Zeppelin500/MBusino/sensostar_dongle/picture2.jpg

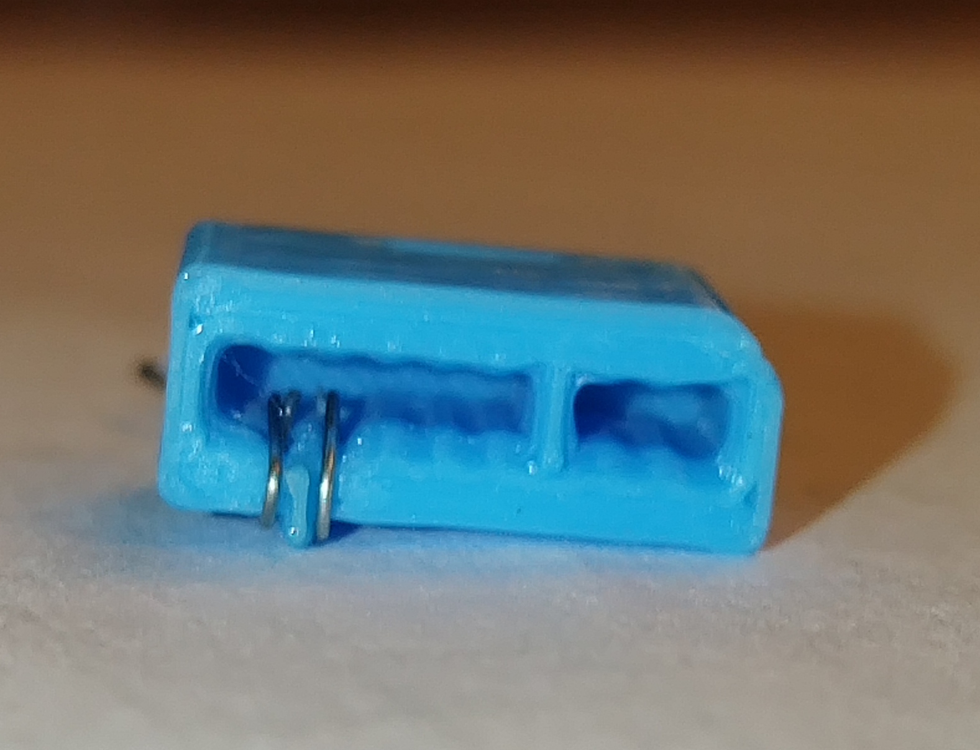
sensostar_dongle/picture2.jpg
