Zeppelin500/MBusino/sensostar_dongle/picture4.jpg

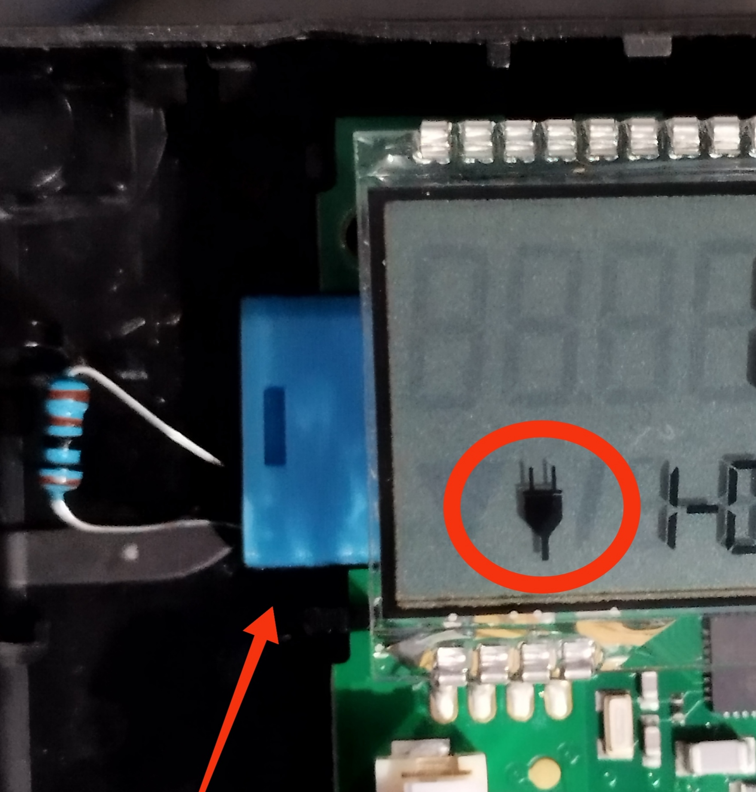
sensostar_dongle/picture4.jpg
