Zeppelin500/MBusino/sensostar_dongle/picture.png

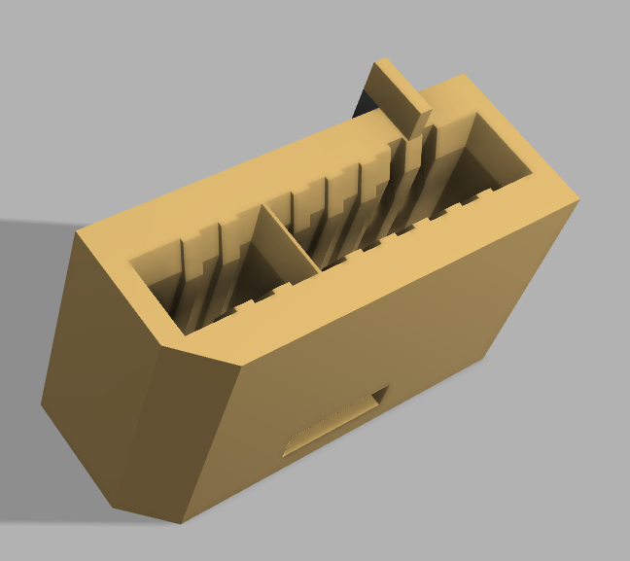
sensostar_dongle/picture.png
