Zeppelin500/MBusino/src/MBusino5S/autodiscover.h

struct autodiscover {
  char bufferValue[1024] = {0};
  char bufferTopic[100] = {0};
  char haName[30] = {0};
  char haUnits[30] = {0};
  char stateClass[30] = {0};
  char deviceClass[30] = {0};
  char deviceClassString[50] = {0};
} adVariables; // home assistand auto discover

const char bmeValue[4][12] = {"temperature","pressure","altitude","humidity"};
const char bmeDeviceClass[4][12] = {"temperature","pressure","distance","humidity"};
const char bmeUnits[4][5] = {"°C","mbar","m","%"};

//const char vs[4] = "_vs"; //placeholder for insert "_vs" for valuestring is used instead of value
//const char[4] noVs = {0}; //empty, no Valuestring

const char adValueMbus[] PROGMEM = R"rawliteral({"unique_id":"%s_%u_%u_%s","default_entity_id":"sensor.%s_%u_%u_%s","state_topic":"%s/MBus/SlaveAddress%u/%u_%s","name":"Addr%u_%u_%s","value_template":"{{value_json}}","unit_of_meas":"%s","state_class":"%s","device":{"ids": ["%s"],"name":"%s","manufacturer": "MBusino","mdl":"V%s"},%s"expire_after":%u,"availability_topic":"%s/status","payload_available":"online","payload_not_available":"offline","availability_mode":"all"})rawliteral";
const char adTopicMbus[] PROGMEM = R"rawliteral(homeassistant/sensor/%s/%u_%u_%s/config)rawliteral";

const char adValueSensor[] PROGMEM = R"rawliteral({"unique_id":"%s_Sensor%u","default_entity_id":"sensor.%s_Sensor%u","state_topic":"%s/OneWire/S%u","name":"Sensor%u","value_template":"{{value_json}}","unit_of_meas":"°C","state_class":"measurement","device":{"ids": ["%s"],"name":"%s","manufacturer": "MBusino","mdl":"V%s"},"device_class":"temperature","expire_after":%u,"availability_topic":"%s/status","payload_available":"online","payload_not_available":"offline","availability_mode":"all"})rawliteral";
const char adTopicSensor[] PROGMEM = R"rawliteral(homeassistant/sensor/%s/Sensor%u/config)rawliteral";

const char adValueBME[] PROGMEM = R"rawliteral({"unique_id":"%s__BME_%s","default_entity_id":"sensor.%s_BME_%s","state_topic":"%s/bme/%s","name":"%s","value_template":"{{value_json}}","unit_of_meas":"%s","state_class":"measurement","device":{"ids": ["%s"],"name":"%s","manufacturer": "MBusino","mdl":"V%s"},"device_class":"%s","expire_after":%u,"availability_topic":"%s/status","payload_available":"online","payload_not_available":"offline","availability_mode":"all"})rawliteral";
const char adTopicBME[] PROGMEM = R"rawliteral(homeassistant/sensor/%s/%s/config)rawliteral";

void haHandoverMbus(uint8_t haCounter, bool engelmann, uint8_t address){ // haCounter is the "i+1" at the for() in main

  if(adVariables.deviceClass[0] != 0){
    strcpy(adVariables.deviceClassString,String("\"device_class\": \"" + String(adVariables.deviceClass) + "\",").c_str());
  }
  sprintf(adVariables.bufferValue,adValueMbus,userData.mbusinoName,address,haCounter,adVariables.haName,userData.mbusinoName,address,haCounter,adVariables.haName,userData.mbusinoName,address,haCounter,adVariables.haName,address,haCounter,adVariables.haName,adVariables.haUnits,adVariables.stateClass,userData.mbusinoName,userData.mbusinoName,MBUSINO_VERSION,adVariables.deviceClassString,userData.mbusInterval / 1000 * 3 * (userData.mbusSlaves > 0 ? userData.mbusSlaves : 1),userData.mbusinoName);
  sprintf(adVariables.bufferTopic,adTopicMbus,userData.mbusinoName,address,haCounter,adVariables.haName);
  client.publish(adVariables.bufferTopic, adVariables.bufferValue, true); 

  if(haCounter == 4 && engelmann == true){  // Sensostar Bugfix --> comment it out if you use not a Sensostar   
    sprintf(adVariables.bufferValue,adValueMbus,userData.mbusinoName,address,haCounter,"power_calc",userData.mbusinoName,address,haCounter,"power_calc",userData.mbusinoName,address,haCounter,"power_calc",address,haCounter,"power_calc",adVariables.haUnits,adVariables.stateClass,userData.mbusinoName,userData.mbusinoName,MBUSINO_VERSION,adVariables.deviceClassString,userData.mbusInterval / 1000 * 3 * (userData.mbusSlaves > 0 ? userData.mbusSlaves : 1),userData.mbusinoName);
    sprintf(adVariables.bufferTopic,adTopicMbus,userData.mbusinoName,address,haCounter,"power_calc");
    client.publish(adVariables.bufferTopic, adVariables.bufferValue, true);                   
  } 

  adVariables.bufferTopic[0] = 0;
  adVariables.bufferValue[0] = 0;
  adVariables.deviceClass[0] = 0;
  adVariables.deviceClassString[0] = 0;
  adVariables.stateClass[0] = 0;
  adVariables.haUnits[0] = 0;
}

void haHandoverOw(uint8_t haCounter){
  sprintf(adVariables.bufferValue,adValueSensor,userData.mbusinoName,haCounter,userData.mbusinoName,haCounter,userData.mbusinoName,haCounter,haCounter,userData.mbusinoName,userData.mbusinoName,MBUSINO_VERSION,userData.sensorInterval / 1000 * 3,userData.mbusinoName);
  sprintf(adVariables.bufferTopic,adTopicSensor,userData.mbusinoName,haCounter);
  client.publish(adVariables.bufferTopic, adVariables.bufferValue, true); 
  adVariables.bufferTopic[0] = 0;
  adVariables.bufferValue[0] = 0;
}

void haHandoverBME(){
  for(uint8_t i=0; i<4;i++){  
    sprintf(adVariables.bufferValue,adValueBME,userData.mbusinoName,bmeValue[i],userData.mbusinoName,bmeValue[i],userData.mbusinoName,bmeValue[i],bmeValue[i],bmeUnits[i],userData.mbusinoName,userData.mbusinoName,MBUSINO_VERSION,bmeDeviceClass[i],userData.sensorInterval / 1000 * 3,userData.mbusinoName);
    sprintf(adVariables.bufferTopic,adTopicBME,userData.mbusinoName,bmeValue[i]);
    client.publish(adVariables.bufferTopic, adVariables.bufferValue, true); 
    adVariables.bufferTopic[0] = 0;
    adVariables.bufferValue[0] = 0;
  }
}

// --- Header autodiscovery ---
struct headerAdField {
  const char* jsonKey;
};

static const headerAdField headerAdFields[] = {
  {"address"},
  {"id"},
  {"manufacturer"},
  {"medium"},
  {"version"},
  {"status"},
  {"access_counter"},
  {"battery_low"},
  {"temporary_error"},
  {"permanent_error"},
};

#define HEADER_AD_FIELDS_COUNT (sizeof(headerAdFields) / sizeof(headerAdFields[0]))

const char adValueHeader[] PROGMEM = R"rawliteral({"unique_id":"%s_header_%u_%s","default_entity_id":"sensor.%s_header_%u_%s","state_topic":"%s/MBus/SlaveAddress%u/header/%s","name":"Addr%u_%s","value_template":"{{value}}","device":{"ids": ["%s"],"name":"%s","manufacturer": "MBusino","mdl":"V%s"},"availability_topic":"%s/status","payload_available":"online","payload_not_available":"offline","availability_mode":"all"})rawliteral";
const char adTopicHeader[] PROGMEM = R"rawliteral(homeassistant/sensor/%s/header_%u_%s/config)rawliteral";

void haHandoverHeader(uint8_t address){
  for(uint8_t i = 0; i < HEADER_AD_FIELDS_COUNT; i++){
    sprintf(adVariables.bufferValue, adValueHeader,
      userData.mbusinoName, address, headerAdFields[i].jsonKey,
      userData.mbusinoName, address, headerAdFields[i].jsonKey,
      userData.mbusinoName, address, headerAdFields[i].jsonKey,
      address, headerAdFields[i].jsonKey,
      userData.mbusinoName, userData.mbusinoName, MBUSINO_VERSION,
      userData.mbusinoName);
    sprintf(adVariables.bufferTopic, adTopicHeader, userData.mbusinoName, address, headerAdFields[i].jsonKey);
    client.publish(adVariables.bufferTopic, adVariables.bufferValue, true);
    adVariables.bufferTopic[0] = 0;
    adVariables.bufferValue[0] = 0;
  }
}

// --- Header MQTT publish ---
enum HeaderFieldType { HT_STR, HT_INT, HT_HEX, HT_BOOL_NESTED };

struct headerPublishField {
  const char* jsonKey;
  HeaderFieldType type;
};

static const headerPublishField headerPublishFields[] = {
  {"address",        HT_INT},
  {"id",             HT_STR},
  {"manufacturer",   HT_STR},
  {"medium",         HT_STR},
  {"version",        HT_INT},
  {"status",         HT_HEX},
  {"access_counter", HT_INT},
};

#define HEADER_PUBLISH_COUNT (sizeof(headerPublishFields) / sizeof(headerPublishFields[0]))

static const char* headerStatusKeys[] = {"battery_low", "temporary_error", "permanent_error"};
#define HEADER_STATUS_COUNT (sizeof(headerStatusKeys) / sizeof(headerStatusKeys[0]))



/*
char* getStateClass(const char* unit) {
  if (this->unit == "C") {
      return "measurement";
  }else if (this->unit == "K") {
      return "measurement";
  }else if (this->unit == "W") {
      return "measurement";
  }else if(this->unit =="Wh") {
      return "total";
  }else if(this->unit=="kWh"){
      return "total";
  }else if(this->unit=="m3") {
      return "total";
  }else if(this->unit =="m3/h"){
      return "measurement";
  } else {
      return String("");
  }
}

String getDeviceClass() {
    if (this->unit == "C") {
        return "temperature";
    }else if (this->unit == "K") {
        return "temperature";
    }else if (this->unit == "W") {
        return "power";
    }else if(this->unit =="Wh") {
        return "energy";
    }else if(this->unit=="kWh"){
        return "energy";
    }else if(this->unit=="m3") {
        return "water";
    }else if(this->unit =="m3/h"){
        return String("");
    } else {
        return String("");
    }
}


///######## Device.h #####################################
#include <vector>
class Device {
public:

    Device() = default;
    String toJsonString(String mbusinoName) const {
        String oss;
        oss +=  "{";
        oss +=   "\"ids\":  [";
        oss +=    "\""+mbusinoName+"\"";
        oss +=    "],";
        oss +=    "\"name\": \""+mbusinoName+"\",";
        oss +=    "\"mdl\": \"MBusino v.070\"";
        oss += "}";
        return oss;
    }
};

///######## MBusTopic.h #####################################
#include "SensorData.h"

class MBusTopic {
public:
    String topic;
    String value;
    String unit;
    String name;

    MBusTopic(String t) : topic(t), value(""), unit("") {
        name = getLastTopicPart(t);
    }

    void setValue(String v) {
        value = v;
    }

    void setUnit(String u) {
        unit = u;
    }

private:
    const char *getLastTopicPart(String curTopic) {
        const char *lastSlash = strrchr(curTopic.c_str(), '/'); // Suche den letzten Slash

        if (lastSlash != nullptr) {
            // Rückgabe des Zeigers auf den Anfang des letzten Teils des Topics
            return lastSlash + 1;
        } else {
            // Wenn kein Slash gefunden wurde, bedeutet das, dass der ganze String das Topic ist
            return curTopic.c_str();
        }
    }

    bool isValid() {
        if (this->value != nullptr && this->unit != nullptr) {
            return true;
        } else {
            return false;
        }
    }

private:
    String getUnitOfMeassuremetn() {
        if (this->unit == "C") {
            return "°C";
        }else if (this->unit == "K") {
            return "K";
        }else if (this->unit == "W") {
            return "W";
        }else if(this->unit =="Wh") {
            return "Wh";
        }else if(this->unit=="kWh"){
            return "kWh";
        }else if(this->unit=="m3") {
            return "m³";
        }else if(this->unit =="m3/h"){
            return "m³/h";
        } else {
            return String("");
        }
    }
private:
    String getStateClass() {
        if (this->unit == "C") {
            return "measurement";
        }else if (this->unit == "K") {
            return "measurement";
        }else if (this->unit == "W") {
            return "measurement";
        }else if(this->unit =="Wh") {
            return "total";
        }else if(this->unit=="kWh"){
            return "total";
        }else if(this->unit=="m3") {
            return "total";
        }else if(this->unit =="m3/h"){
            return "measurement";
        } else {
            return String("");
        }
    }
private:
    String getDeviceClass() {
        if (this->unit == "C") {
            return "temperature";
        }else if (this->unit == "K") {
            return "temperature";
        }else if (this->unit == "W") {
            return "power";
        }else if(this->unit =="Wh") {
            return "energy";
        }else if(this->unit=="kWh"){
            return "energy";
        }else if(this->unit=="m3") {
            return "water";
        }else if(this->unit =="m3/h"){
            return String("");
        } else {
            return String("");
        }
    }


public:
    SensorData toSensorData(String basic) {
        SensorData sensorData;
        sensorData.unique_id = basic + "_" + this->name;
        sensorData.object_id = basic + "_" + this->name;
        sensorData.state_topic = this->topic;
        sensorData.name = this->name;
        sensorData.value_template = "{{value_json if value_json is defined else 0}}";
        sensorData.unit_of_meas = getUnitOfMeassuremetn();
        sensorData.state_class = getStateClass();
        sensorData.device_class = getDeviceClass();
        sensorData.availability_mode = "all";
        return sensorData;
    }
};

///######## MBusTopicService.h #####################################
#include "SensorData.h"

class MBusTopic {
public:
    String topic;
    String value;
    String unit;
    String name;

    MBusTopic(String t) : topic(t), value(""), unit("") {
        name = getLastTopicPart(t);
    }

    void setValue(String v) {
        value = v;
    }

    void setUnit(String u) {
        unit = u;
    }

private:
    const char *getLastTopicPart(String curTopic) {
        const char *lastSlash = strrchr(curTopic.c_str(), '/'); // Suche den letzten Slash

        if (lastSlash != nullptr) {
            // Rückgabe des Zeigers auf den Anfang des letzten Teils des Topics
            return lastSlash + 1;
        } else {
            // Wenn kein Slash gefunden wurde, bedeutet das, dass der ganze String das Topic ist
            return curTopic.c_str();
        }
    }

    bool isValid() {
        if (this->value != nullptr && this->unit != nullptr) {
            return true;
        } else {
            return false;
        }
    }

private:
    String getUnitOfMeassuremetn() {
        if (this->unit == "C") {
            return "°C";
        }else if (this->unit == "K") {
            return "K";
        }else if (this->unit == "W") {
            return "W";
        }else if(this->unit =="Wh") {
            return "Wh";
        }else if(this->unit=="kWh"){
            return "kWh";
        }else if(this->unit=="m3") {
            return "m³";
        }else if(this->unit =="m3/h"){
            return "m³/h";
        } else {
            return String("");
        }
    }
private:
    String getStateClass() {
        if (this->unit == "C") {
            return "measurement";
        }else if (this->unit == "K") {
            return "measurement";
        }else if (this->unit == "W") {
            return "measurement";
        }else if(this->unit =="Wh") {
            return "total";
        }else if(this->unit=="kWh"){
            return "total";
        }else if(this->unit=="m3") {
            return "total";
        }else if(this->unit =="m3/h"){
            return "measurement";
        } else {
            return String("");
        }
    }
private:
    String getDeviceClass() {
        if (this->unit == "C") {
            return "temperature";
        }else if (this->unit == "K") {
            return "temperature";
        }else if (this->unit == "W") {
            return "power";
        }else if(this->unit =="Wh") {
            return "energy";
        }else if(this->unit=="kWh"){
            return "energy";
        }else if(this->unit=="m3") {
            return "water";
        }else if(this->unit =="m3/h"){
            return String("");
        } else {
            return String("");
        }
    }


public:
    SensorData toSensorData(String basic) {
        SensorData sensorData;
        sensorData.unique_id = basic + "_" + this->name;
        sensorData.object_id = basic + "_" + this->name;
        sensorData.state_topic = this->topic;
        sensorData.name = this->name;
        sensorData.value_template = "{{value_json if value_json is defined else 0}}";
        sensorData.unit_of_meas = getUnitOfMeassuremetn();
        sensorData.state_class = getStateClass();
        sensorData.device_class = getDeviceClass();
        sensorData.availability_mode = "all";
        return sensorData;
    }
};
//######################### SensorData.h ###############################################################
#include <vector>
#include "Device.h"

class SensorData {
public:
    String unique_id;
    String object_id;
    String state_topic;
    String name;
    String value_template;
    String unit_of_meas;
    String state_class;
    Device device;
    String availability_mode;
    String device_class;

    SensorData() = default;

public:
    String toJsonString(String mbusinoName) const {
        String oss;
        oss += "{";
        oss += "\"unique_id\":\"" + unique_id + "\",";
        oss += "\"object_id\":\"" + object_id + "\",";
        oss += "\"state_topic\":\"" + state_topic + "\",";
        oss += "\"name\":\"" + name + "\",";
        oss += "\"value_template\":\"" + value_template + "\",";
        if (!unit_of_meas.isEmpty()) {
            oss += "\"unit_of_meas\":\"" + unit_of_meas + "\",";
        }
        // checking state_class for null and empty, if nothing is present then no entry is made in JSON
        if (!state_class.isEmpty()) {
            oss += "\"state_class\":\"" + state_class + "\",";
        }
        oss += "\"device\":" + device.toJsonString(mbusinoName) + ",";
        if (!device_class.isEmpty()) {
            oss += "\"device_class\":\"" + device_class+ "\",";
        }
        oss += "\"availability_mode\":\"" + availability_mode + "\"";

        oss += "}";
        return oss;
    }

};
*/
