Zeppelin500/MBusino/src/MBusinoNano5S/networkEvents.h

// WARNING: onEvent is called from a separate FreeRTOS task (thread)!
void onEvent(arduino_event_id_t event) {
  switch (event) {
    case ARDUINO_EVENT_ETH_START:
      Serial.println("ETH Started");
      // The hostname must be set after the interface is started, but needs
      // to be set before DHCP, so set it from the event handler thread.
//      ETH.setHostname(String(String(userData.mbusinoName)+"-eth").c_str());
      ETH.setHostname(userData.mbusinoName);
      //ETH.setLinkSpeed(10);
      break;
    case ARDUINO_EVENT_ETH_CONNECTED: 
      Serial.println("ETH Connected"); 
      eth_connected = true;
      timerETHmessage = millis();
      timerNetworkChange = millis();
      break;
    case ARDUINO_EVENT_ETH_GOT_IP:
      Serial.println("ETH Got IP");
      Serial.println(ETH);
      eth_connected = true;
      gotIP = true;
      break;
    case ARDUINO_EVENT_ETH_LOST_IP:
      Serial.println("ETH Lost IP");
      eth_connected = false;
      Serial.println("Lost ETH IP, restart soon");
      timerReboot = millis();
      waitForRestart = true;
      break;
    case ARDUINO_EVENT_ETH_DISCONNECTED:
      Serial.println("ETH Disconnected");
      eth_connected = false;
      gotIP = false;
      break;
    case ARDUINO_EVENT_ETH_STOP:
      Serial.println("ETH Stopped");
      eth_connected = false;
      break;
    default: break;
  }
}


// WARNING: This function is called from a separate FreeRTOS task (thread)!
void WiFiEvent(WiFiEvent_t event) {
  Serial.printf("[WiFi-event] event: %d\n", event);

  switch (event) {
    case ARDUINO_EVENT_WIFI_READY:               Serial.println("WiFi interface ready"); break;
    case ARDUINO_EVENT_WIFI_SCAN_DONE:           Serial.println("Completed scan for access points"); break;
    case ARDUINO_EVENT_WIFI_STA_START:           Serial.println("WiFi client started"); break;
    case ARDUINO_EVENT_WIFI_STA_STOP:            Serial.println("WiFi clients stopped"); break;
    case ARDUINO_EVENT_WIFI_STA_CONNECTED:
      Serial.println("Connected to access point"); 
      break;
    case ARDUINO_EVENT_WIFI_STA_DISCONNECTED:    
      Serial.println("Disconnected from WiFi access point"); 
      wifiReconnect = true;
      timerWifiReconnect = millis();
    case ARDUINO_EVENT_WIFI_STA_AUTHMODE_CHANGE: Serial.println("Authentication mode of access point has changed"); break;
    case ARDUINO_EVENT_WIFI_STA_GOT_IP:
      Serial.print("Obtained IP address: ");
      Serial.println(WiFi.localIP());
      break;
    case ARDUINO_EVENT_WIFI_STA_LOST_IP:        Serial.println("Lost IP address and IP address is reset to 0"); break;
    case ARDUINO_EVENT_WPS_ER_SUCCESS:          Serial.println("WiFi Protected Setup (WPS): succeeded in enrollee mode"); break;
    case ARDUINO_EVENT_WPS_ER_FAILED:           Serial.println("WiFi Protected Setup (WPS): failed in enrollee mode"); break;
    case ARDUINO_EVENT_WPS_ER_TIMEOUT:          Serial.println("WiFi Protected Setup (WPS): timeout in enrollee mode"); break;
    case ARDUINO_EVENT_WPS_ER_PIN:              Serial.println("WiFi Protected Setup (WPS): pin code in enrollee mode"); break;
    case ARDUINO_EVENT_WIFI_AP_START:           Serial.println("WiFi access point started"); break;
    case ARDUINO_EVENT_WIFI_AP_STOP:            Serial.println("WiFi access point  stopped"); break;
    case ARDUINO_EVENT_WIFI_AP_STACONNECTED:    Serial.println("Client connected"); break;
    case ARDUINO_EVENT_WIFI_AP_STADISCONNECTED: Serial.println("Client disconnected"); break;
    case ARDUINO_EVENT_WIFI_AP_STAIPASSIGNED:   Serial.println("Assigned IP address to client"); break;
    case ARDUINO_EVENT_WIFI_AP_PROBEREQRECVED:  Serial.println("Received probe request"); break;
    case ARDUINO_EVENT_WIFI_AP_GOT_IP6:         Serial.println("AP IPv6 is preferred"); break;
    case ARDUINO_EVENT_WIFI_STA_GOT_IP6:        Serial.println("STA IPv6 is preferred"); break;
    case ARDUINO_EVENT_ETH_GOT_IP6:             Serial.println("Ethernet IPv6 is preferred"); break;
    case ARDUINO_EVENT_ETH_START:               Serial.println("Ethernet started"); break;
    case ARDUINO_EVENT_ETH_STOP:                Serial.println("Ethernet stopped"); break;
    case ARDUINO_EVENT_ETH_CONNECTED:           Serial.println("Ethernet connected"); break;
    case ARDUINO_EVENT_ETH_DISCONNECTED:        Serial.println("Ethernet disconnected"); break;
    case ARDUINO_EVENT_ETH_GOT_IP:              Serial.println("Obtained IP address"); break;
    default:                                    break;
  }
}
