Zeppelin500/MBusino/playground/multible_slaves/MBusino_naked_scan/MBusino_naked_scan.ino

/*
# MBusino_naked --> only M-Bus 

21 October 2023: new code based at MBusino with payload library. You find the old "Sensostar only" code in archive.

documentation see MBusino

## Licence
****************************************************
This program is free software: you can redistribute it and/or modify it under the terms of the GNU General Public License as published by
the Free Software Foundation, either version 3 of the License, or (at your option) any later version. This program is distributed in the hope that it will be useful,
but WITHOUT ANY WARRANTY; without even the implied warranty of MERCHANTABILITY or FITNESS FOR A PARTICULAR PURPOSE.  See the GNU General Public License for more details.
You should have received a copy of the GNU General Public License along with this program.  If not, see <http://www.gnu.org/licenses/>.
****************************************************
*/

#include <EspMQTTClient.h>

#include <credentials.h>  // <-- comment it out if you use no library for WLAN access data.

#include <MBusinoLib.h>  // Library for decode M-Bus
#include "ArduinoJson.h"
#include <EEPROM.h>

#define MBUSINO_NAME "SBusino" // If you have more MBusinos, rename it inside quote marks, or it cause some network and MQTT problems. Also you cant reach your MBusino from Arduino IDE

#define MBUS_BAUD_RATE 2400
#define MBUS_ADDRESS 0xFE  // brodcast
#define MBUS_TIMEOUT 1000  // milliseconds
#define MBUS_DATA_SIZE 510
#define MBUS_GOOD_FRAME true
#define MBUS_BAD_FRAME false

#define MBUS_FRAME_SHORT_START          0x10
#define MBUS_FRAME_LONG_START           0x68
#define MBUS_FRAME_STOP                 0x16

#define MBUS_CONTROL_MASK_SND_NKE       0x40
#define MBUS_CONTROL_MASK_DIR_M2S       0x40
#define MBUS_ADDRESS_NETWORK_LAYER      0xFE

#define MBUS_ACK                        0xE5


EspMQTTClient client(
  WLAN_SSID,       // WLAN-SSID in quote marks "mySSID"
  WLAN_PASSWORD,   // WLAN Password in quote marks "myPassword"
  MQTT_Broker,     // MQTT Broker IP address in quote marks "192.168.x.x"
  "MQTTUsername",  // Can be omitted if not needed
  "MQTTPassword",  // Can be omitted if not needed -- also password for OTA Update with Arduino IDE 2
  MBUSINO_NAME,    // Client name that uniquely identify your device
  1883             // The MQTT port, default to 1883. this line can be omitted
);


unsigned long loop_start = 0;
unsigned long last_loop = 0;
bool firstrun = true;
int Startadd = 0x13;  // Start address for decoding
char jsonstring[6144] = { 0 };

int MbusInterval = 5000;           // interval for MBus request in milliseconds

unsigned long timerMbus = 0;

void mbus_normalize(byte address);
void mbus_request_data(byte address);
void mbus_short_frame(byte address, byte C_field);
bool mbus_get_response(byte *pdata, unsigned char len_pdata);
void calibrationAverage();
void calibrationSensor(uint8_t sensor);
void calibrationValue(float value);
void calibrationBME();
void calibrationSet0();

uint8_t scanAddress = 10;
unsigned long scanTimer = 0;
uint8_t scanned = false;
bool setAdress = true;
unsigned long setTimer = 0;
bool normalize = true;
unsigned long setTimer2 = 0;
bool normalize2 = true;

void setup() {
  Serial.begin(2400, SERIAL_8E1);

  // Optional functionalities of EspMQTTClient
  client.enableHTTPWebUpdater("/update");                                           // Enable the web updater. User and password default to values of MQTTUsername and MQTTPassword. These can be overridded with enableHTTPWebUpdater("user", "password").
  client.enableOTA();                                                      // Enable OTA (Over The Air) updates. Password defaults to MQTTPassword. Port is the default OTA port. Can be overridden with enableOTA("password", port).
  client.enableLastWillMessage(MBUSINO_NAME"/lastwill", "I am going offline");  // You can activate the retain flag by setting the third parameter to true
  client.setMaxPacketSize(6000);

  scanTimer = millis()+10000;
  

}

// This function is called once everything is connected (Wifi and MQTT)
// WARNING : YOU MUST IMPLEMENT IT IF YOU USE EspMQTTClient
void onConnectionEstablished() {  // send a message to MQTT broker if connected.
  client.publish(MBUSINO_NAME"/start", "bin hoch gefahren, WLAN und MQTT seht ");  
}

void loop() {
  client.loop();  //MQTT Funktion
  loop_start = millis();
   while (Serial.available() && (millis() - setTimer) < 7000) { // Serial buffer leeren
      byte val = Serial.read();
      client.publish(String(MBUSINO_NAME "/serialAviable/recieved_" + String(scanAddress)), String(val)); 
    }
  if((millis() - setTimer) > 7000 && normalize == true){  
    
    mbus_normalize(0xFD);
    client.publish(String(MBUSINO_NAME"/normalize2"), "done");
    normalize = false;
  }
  if((millis() - setTimer2) > 8000 && normalize2 == true){  
    mbus_normalize(0xFD);
    if (Serial.available()) {
      byte val = Serial.read();
      client.publish(String(MBUSINO_NAME "/normalized2/recieved_" + String(scanAddress)), String(val)); 
    }
    client.publish(String(MBUSINO_NAME"/normalize2"), "done");
    normalize2 = false;
  }

  if((millis() - setTimer) > 10000 && setAdress == true){
    mbus_set_address(0x05, 0x00);
    client.publish(String(MBUSINO_NAME"/setAdress"), "done");
    setAdress = false;
    scanTimer = millis(); 
  }
  if((millis() - scanTimer) > 1000 && scanned == false && setAdress == false){
    client.publish(String(MBUSINO_NAME"/scanning/" + String(scanAddress)), "done");  
    mbus_normalize(scanAddress);
    scanTimer = millis(); 
    scanned = true;
  }
  if((millis() - scanTimer) > 1000 && scanned == true && setAdress == false){
    client.publish(String(MBUSINO_NAME "/reading/" + String(scanAddress)), "done");  
    scanTimer = millis();
    if (Serial.available()) {
      byte val = Serial.read();
      client.publish(String(MBUSINO_NAME "/reading/recieved_" + String(scanAddress)), String(val)); 
    }
  scanned = false;
  scanAddress--;
  }
   
 
}

void mbus_normalize(byte address) {
  mbus_short_frame(address,0x40);
}

void mbus_request_data(byte address) {
  mbus_short_frame(address, 0x5b);
}

void mbus_short_frame(byte address, byte C_field) {
  byte data[6];

  data[0] = 0x10;
  data[1] = C_field;
  data[2] = address;
  data[3] = data[1] + data[2];
  data[4] = 0x16;
  data[5] = '\0';

  Serial.write((char *)data,5);
}

bool mbus_get_response(byte *pdata, unsigned char len_pdata) {
  byte bid = 0;             // current byte of response frame
  byte bid_end = 255;       // last byte of frame calculated from length byte sent
  byte bid_checksum = 255;  // checksum byte of frame (next to last)
  byte len = 0;
  byte checksum = 0;
  bool long_frame_found = false;
  bool complete_frame = false;
  bool frame_error = false;

  unsigned long timer_start = millis();
  while (!frame_error && !complete_frame && (millis() - timer_start) < MBUS_TIMEOUT) {
    while (Serial.available()) {
      byte received_byte = (byte)Serial.read();

      // Try to skip noise
      if (bid == 0 && received_byte != 0xE5 && received_byte != 0x68) {
        continue;
      }

      if (bid > len_pdata) {
        return MBUS_BAD_FRAME;
      }
      pdata[bid] = received_byte;

      // Single Character (ACK)
      if (bid == 0 && received_byte == 0xE5) {
        return MBUS_GOOD_FRAME;
      }

      // Long frame start
      if (bid == 0 && received_byte == 0x68) {
        long_frame_found = true;
      }

      if (long_frame_found) {
        // 2nd byte is the frame length
        if (bid == 1) {
          len = received_byte;
          bid_end = len + 4 + 2 - 1;
          bid_checksum = bid_end - 1;
        }

        if (bid == 2 && received_byte != len) {  // 3rd byte is also length, check that its the same as 2nd byte
          frame_error = true;
        }
        if (bid == 3 && received_byte != 0x68) {
          ;  // 4th byte is the start byte again
          frame_error = true;
        }
        if (bid > 3 && bid < bid_checksum) checksum += received_byte;  // Increment checksum during data portion of frame

        if (bid == bid_checksum && received_byte != checksum) {  // Validate checksum
          frame_error = true;
        }
        if (bid == bid_end && received_byte == 0x16) {  // Parse frame if still valid
          complete_frame = true;
        }
      }
      bid++;
    }
  }

  if (complete_frame && !frame_error) {
    return MBUS_GOOD_FRAME;
  } else {
    return MBUS_BAD_FRAME;
  }
}
void mbus_application_reset(byte address) {
  mbus_control_frame(address,0x53,0x50);
}

void mbus_control_frame(byte address, byte C_field, byte CI_field)
{
  byte data[10];
  data[0] = MBUS_FRAME_LONG_START;
  data[1] = 0x03;
  data[2] = 0x03;
  data[3] = MBUS_FRAME_LONG_START;
  data[4] = C_field;
  data[5] = address;
  data[6] = CI_field;
  data[7] = data[4] + data[5] + data[6];
  data[8] = MBUS_FRAME_STOP;
  data[9] = '\0';

  Serial.write((char*)data);
}

void mbus_set_address(byte oldaddress, byte newaddress) {
 
  byte data[13];
 
  data[0] = MBUS_FRAME_LONG_START;
  data[1] = 0x06;
  data[2] = 0x06;
  data[3] = MBUS_FRAME_LONG_START;
  
  data[4] = 0x53;
  data[5] = oldaddress;
  data[6] = 0x51;
  
  data[7] = 0x01;         // DIF [EXT0, LSB0, FN:00, DATA 1 8BIT INT]
  data[8] = 0x7A;         // VIF 0111 1010 bus address
  data[9] = newaddress;   // DATA new address
  
  data[10] = data[4]+data[5]+data[6]+data[7]+data[8]+data[9];
  data[11] = 0x16;
  data[12] = '\0';
  
  Serial.write((char*)data,12);
}
