Zeppelin500/MBusino/playground/MBusino_autodiscovery_mitLib_copy/MBusinoLib/test/aunit/test.cpp

/*

This File is the original File from AllWize, only the Lib name is changed.

----------------------------------------------------------------

MBUS Payload Encoder / Decoder

Unit Tests

Copyright (C) 2019 by AllWize
Copyright (C) 2019 by Xose Pérez <xose at allwize dot io>

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
*/

#include <Arduino.h>
#include "MBusinoLib.h"
#include <AUnit.h>

using namespace aunit;

#define MBUS_PAYLOAD_TEST_VERBOSE 1

#if defined(ARDUINO_ARCH_SAMD)
    #define PC_SERIAL SerialUSB
#else
    #define PC_SERIAL Serial
#endif

// -----------------------------------------------------------------------------
// Wrapper class
// -----------------------------------------------------------------------------

class MBusinoLibWrap: public MBusinoLib {
    
    public:
        
        MBusinoLibWrap() : MBusinoLib() {}
        MBusinoLibWrap(uint8_t size) : MBusinoLib(size) {}
        int8_t findDefinition(uint32_t vif) { return _findDefinition(vif); }
        uint32_t getVIF(uint8_t code, int8_t scalar) { return _getVIF(code, scalar); }

};

// -----------------------------------------------------------------------------
// Helper methods
// -----------------------------------------------------------------------------

class EncoderTest: public TestOnce {

    protected:

        virtual void setup() override {
            MBusinoLib = new MBusinoLibWrap();
            MBusinoLib->reset();
        }

        virtual void teardown() override {
            delete MBusinoLib;
        }

        virtual void compare(unsigned char depth, uint8_t * expected) {
            
            uint8_t * actual = MBusinoLib->getBuffer();
            
            #if MBUS_PAYLOAD_TEST_VERBOSE
                PC_SERIAL.println();
                char buff[6];
                PC_SERIAL.print("Expected: ");
                for (unsigned char i=0; i<depth; i++) {
                    snprintf(buff, sizeof(buff), "%02X ", expected[i]);
                    PC_SERIAL.print(buff);
                }
                PC_SERIAL.println();
                PC_SERIAL.print("Actual  : ");
                for (unsigned char i=0; i<MBusinoLib->getSize(); i++) {
                    snprintf(buff, sizeof(buff), "%02X ", actual[i]);
                    PC_SERIAL.print(buff);
                }
                PC_SERIAL.println();
            #endif

            assertEqual(depth, MBusinoLib->getSize());
            for (unsigned char i=0; i<depth; i++) {
                assertEqual(expected[i], actual[i]);
            }

        }

        MBusinoLibWrap * MBusinoLib;

};

class DecoderTest: public TestOnce {

    protected:

        virtual void setup() override {
            MBusinoLib = new MBusinoLibWrap(10);
            MBusinoLib->reset();
        }

        virtual void teardown() override {
            delete MBusinoLib;
        }

        virtual void compare(uint8_t * buffer, unsigned char len, uint8_t fields, uint8_t code = 0xFF, int8_t scalar = 0, uint32_t value = 0) {
            
            DynamicJsonDocument jsonBuffer(256);
            JsonArray root = jsonBuffer.createNestedArray();    
            assertEqual(fields, MBusinoLib->decode(buffer, len, root));
            assertEqual(fields, (uint8_t) root.size());

            #if MBUS_PAYLOAD_TEST_VERBOSE
                PC_SERIAL.println();
                serializeJsonPretty(root, PC_SERIAL);
                PC_SERIAL.println();
            #endif

            if (code != 0xFF) {
                assertEqual(code, (uint8_t) root[0]["code"]);
                assertEqual(scalar, (int8_t) root[0]["scalar"]);
                assertEqual(value, (uint32_t) root[0]["value_raw"]);
            }

        }

        MBusinoLibWrap * MBusinoLib;
        

};

// -----------------------------------------------------------------------------
// Tests
// -----------------------------------------------------------------------------

testF(EncoderTest, Empty) {
    MBusinoLib->reset();
    assertEqual(0, MBusinoLib->getSize());
}

testF(EncoderTest, Unsupported_Coding) {
    MBusinoLib->addRaw(0x0F, 0x06, 14);
    assertEqual(MBUS_ERROR::UNSUPPORTED_CODING, MBusinoLib->getError());
    assertEqual(MBUS_ERROR::NO_ERROR, MBusinoLib->getError());
}

testF(EncoderTest, Add_Raw_8bit) {
    uint8_t expected[] = { 0x01, 0x06, 0x0E};
    MBusinoLib->addRaw(MBUS_CODING::BIT_8, 0x06, 14);
    compare(sizeof(expected), expected);
}

testF(EncoderTest, Add_Raw_16bit) {
    uint8_t expected[] = { 0x02, 0x06, 0x0E, 0x00};
    MBusinoLib->addRaw(MBUS_CODING::BIT_16, 0x06, 14);
    compare(sizeof(expected), expected);
}

testF(EncoderTest, Add_Raw_32bit) {
    uint8_t expected[] = { 0x04, 0x06, 0x0E, 0x00, 0x00, 0x00};
    MBusinoLib->addRaw(MBUS_CODING::BIT_32, 0x06, 14);
    compare(sizeof(expected), expected);
}

testF(EncoderTest, Add_Raw_2bcd) {
    uint8_t expected[] = { 0x09, 0x06, 0x14};
    MBusinoLib->addRaw(MBUS_CODING::BCD_2, 0x06, 14);
    compare(sizeof(expected), expected);
}

testF(EncoderTest, Add_Raw_8bcd) {
    uint8_t expected[] = { 0x0C, 0x13, 0x13, 0x20, 0x00, 0x00};
    MBusinoLib->addRaw(MBUS_CODING::BCD_8, 0x13, 2013);
    compare(sizeof(expected), expected);
}

testF(EncoderTest, Add_Raw_VIFE) {
    uint8_t expected[] = { 0x01, 0xFB, 0x8C, 0x74, 0x0E};
    MBusinoLib->addRaw(MBUS_CODING::BIT_8, 0xFB8C74, 14);
    compare(sizeof(expected), expected);
}

testF(EncoderTest, Find_Definition) {
    assertEqual((int8_t) 0, MBusinoLib->findDefinition(0x03));
}

testF(EncoderTest, Get_VIF) {
    assertEqual((uint32_t) 0xFF  , MBusinoLib->getVIF(MBUS_CODE::ENERGY_WH, -4));
    assertEqual((uint32_t) 0x00  , MBusinoLib->getVIF(MBUS_CODE::ENERGY_WH, -3));
    assertEqual((uint32_t) 0x03  , MBusinoLib->getVIF(MBUS_CODE::ENERGY_WH,  0));
    assertEqual((uint32_t) 0x06  , MBusinoLib->getVIF(MBUS_CODE::ENERGY_WH,  3));
    assertEqual((uint32_t) 0x07  , MBusinoLib->getVIF(MBUS_CODE::ENERGY_WH,  4));
    assertEqual((uint32_t) 0xFB00, MBusinoLib->getVIF(MBUS_CODE::ENERGY_WH,  5));
    assertEqual((uint32_t) 0xFB01, MBusinoLib->getVIF(MBUS_CODE::ENERGY_WH,  6));
    assertEqual((uint32_t) 0xFF  , MBusinoLib->getVIF(MBUS_CODE::ENERGY_WH,  7));
}

testF(EncoderTest, Add_Field_1a) {
    uint8_t expected[] = { 0x02, 0x06, 0x78, 0x05 };
    MBusinoLib->addField(MBUS_CODE::ENERGY_WH, 3, 1400); // 1400 kWh
    compare(sizeof(expected), expected);
}

testF(EncoderTest, Add_Field_1b) {
    uint8_t expected[] = { 0x01, 0x07, 0x8C };
    MBusinoLib->addField(MBUS_CODE::ENERGY_WH, 4, 140); // 1400 kWh
    compare(sizeof(expected), expected);
}

testF(EncoderTest, Add_Field_2) {
    uint8_t expected[] = { 0x01, 0xFB, 0x01, 0xC8 };
    MBusinoLib->addField(MBUS_CODE::ENERGY_WH, 6, 200); // 200 MWh
    compare(sizeof(expected), expected);
}

testF(EncoderTest, Add_Field_3) {
    uint8_t expected[] = { 0x01, 0x0D, 0x24 };
    MBusinoLib->addField(MBUS_CODE::ENERGY_J, 5, 36); // 3.6 MJ
    compare(sizeof(expected), expected);
}

testF(EncoderTest, Add_Field_4) {
    uint8_t expected[] = { 0x01, 0x13, 0x39 };
    MBusinoLib->addField(MBUS_CODE::VOLUME_M3, -3, 57); // 57 l
    compare(sizeof(expected), expected);
}

testF(EncoderTest, MultiField) {
    uint8_t expected[] = { 0x01, 0x13, 0x39, 0x01, 0x0D, 0x24 };
    MBusinoLib->addField(MBUS_CODE::VOLUME_M3, -3, 57); // 57 l
    MBusinoLib->addField(MBUS_CODE::ENERGY_J, 5, 36); // 3.6 MJ
    compare(sizeof(expected), expected);
}

testF(EncoderTest, Add_Field_Compact_1) {
    uint8_t expected[] = { 0x01, 0x13, 0x39 };
    MBusinoLib->addField(MBUS_CODE::VOLUME_M3, 0.057); // 57 l
    compare(sizeof(expected), expected);
}

testF(EncoderTest, Add_Field_Compact_2) {
    uint8_t expected[] = { 0x01, 0x0D, 0x24 };
    MBusinoLib->addField(MBUS_CODE::ENERGY_J, 36e5); // 3.6 MJ
    compare(sizeof(expected), expected);
}

testF(EncoderTest, Add_Field_Compact_3) {
    uint8_t expected[] = { 0x02, 0x2A, 0x06, 0x05 };
    MBusinoLib->addField(MBUS_CODE::POWER_W, 128.6); // 128.6 W
    compare(sizeof(expected), expected);
}

testF(EncoderTest, Add_Field_Compact_Zero) {
    uint8_t expected[] = { 0x01, 0x2B, 0x00 };
    MBusinoLib->addField(MBUS_CODE::POWER_W, 0); // 0 W
    compare(sizeof(expected), expected);
}

testF(EncoderTest, Add_Field_Compact_Infinite_Decimals) {
    uint8_t expected[] = { 0x01, 0x69, 0x67 };
    MBusinoLib->addField(MBUS_CODE::PRESSURE_BAR, 1.02999999999999999); // 1.03 bars
    compare(sizeof(expected), expected);
}

// -----------------------------------------------------------------------------
testF(DecoderTest, Number_1) {
    uint8_t buffer[] = { 0x01, 0xFB, 0x01, 0xC8};
    compare(buffer, sizeof(buffer), 1, MBUS_CODE::ENERGY_WH, 6, 200);
}

testF(DecoderTest, Number_2) {
    uint8_t buffer[] = { 0x01, 0x13, 0x39 };
    compare(buffer, sizeof(buffer), 1, MBUS_CODE::VOLUME_M3, -3, 57);
}

testF(DecoderTest, Number_3) {
    uint8_t buffer[] = { 0x02, 0x06, 0x78, 0x05 };
    compare(buffer, sizeof(buffer), 1, MBUS_CODE::ENERGY_WH, 3, 1400);
}

testF(DecoderTest, Number_4) {
    uint8_t buffer[] = { 0x01, 0x07, 0x8C };
    compare(buffer, sizeof(buffer), 1, MBUS_CODE::ENERGY_WH, 4, 140);
}

testF(DecoderTest, Number_5) {
    uint8_t buffer[] = { 0x01, 0xFB, 0x01, 0xC8 };
    compare(buffer, sizeof(buffer), 1, MBUS_CODE::ENERGY_WH, 6, 200);
}

testF(DecoderTest, Number_6) {
    uint8_t buffer[] = { 0x01, 0x2B, 0x00 };
    compare(buffer, sizeof(buffer), 1, MBUS_CODE::POWER_W, 0, 0);
}

testF(DecoderTest, MultiField) {
    uint8_t buffer[] = { 0x01, 0x13, 0x39, 0x01, 0x0D, 0x24 };
    compare(buffer, sizeof(buffer), 2, MBUS_CODE::VOLUME_M3, -3, 57);
}

testF(DecoderTest, Decode_2bcd) {
    uint8_t buffer[] = { 0x09, 0x06, 0x14};
    compare(buffer, sizeof(buffer), 1, MBUS_CODE::ENERGY_WH, 3, 14);
}

testF(DecoderTest, Decode_8bcd) {
    uint8_t buffer[] = { 0x0C, 0x13, 0x13, 0x20, 0x00, 0x00};
    compare(buffer, sizeof(buffer), 1, MBUS_CODE::VOLUME_M3, -3, 2013);
}

// -----------------------------------------------------------------------------
// Main
// -----------------------------------------------------------------------------

void setup() {

    PC_SERIAL.begin(115200);
    while (!PC_SERIAL && millis() < 5000);

    Printer::setPrinter(&PC_SERIAL);
    //TestRunner::setVerbosity(Verbosity::kAll);

}

void loop() {
    TestRunner::run();
    delay(1);
}
